ChrisBaehrig/cnc-wire-bender/Mechanical_parts/Schlitten-Halter-Heber v2.stl

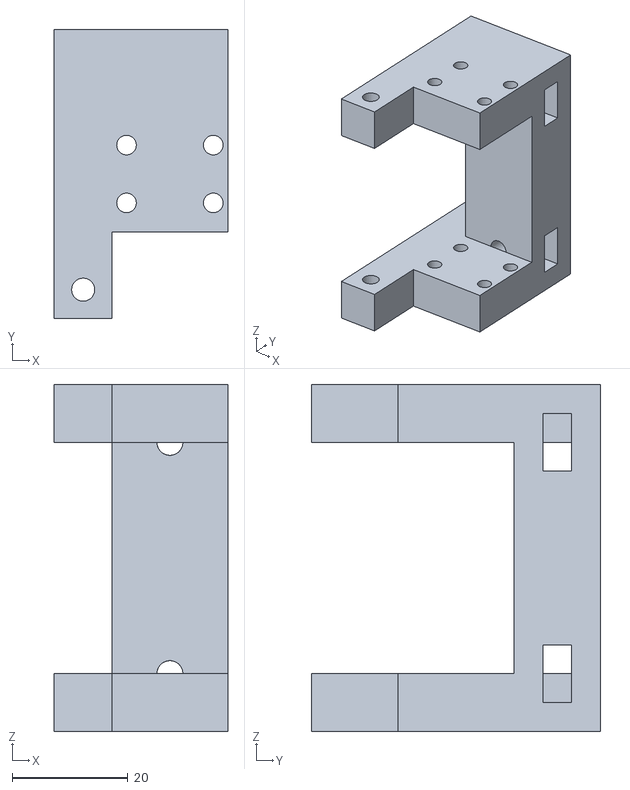
[picture p15: CAD file, 2022-11-18]
Mechanical_parts/Schlitten-Halter-Heber v2.stl
30.0 x 50.0 x 60.0
