ChrisBaehrig/cnc-wire-bender/Mechanical_parts/Düse v5.stl

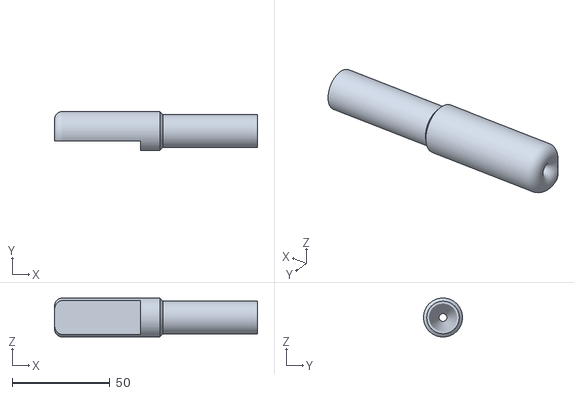
[picture p16: CAD file, 2022-11-18]
Mechanical_parts/Düse v5.stl
104.0 x 20.0 x 20.0
