ChrisBaehrig/cnc-wire-bender/Mechanical_parts/Gegenhalter-Vorschub v6.3mf

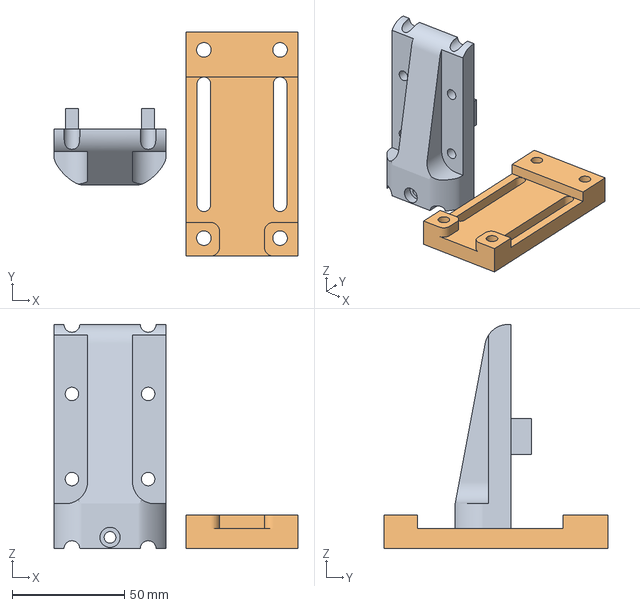
[picture p17: CAD file, 2025-04-29, an earlier design]
Mechanical_parts/Gegenhalter-Vorschub v6.3mf
108.9 x 100.0 x 100.0 mm
Körper3
Körper1
